kylebernier/lambda-oxygen-sensor-interface/verification/DAC_air_comp.csv

#Digilent WaveForms Oscilloscope Acquisition
#Device Name: Discovery2
#Serial Number: SN:210321A36376
#Date Time: 2019-03-14 15:58:00.707
#Sample rate: 800000Hz
#Samples: 8192
#Trigger: Source: Channel 1 Type: Edge Condition: Rising Level: 2.95 V Hyst.: Auto HoldOff: 0 s
#Channel 1: Range: 500 mV/div Offset: -500 mV
#Channel 2: Range: 500 mV/div Offset: -500 mV
#Math 2: Function: (C1-C2)/0.00017053
Time (s) | Channel 1 (V) | Channel 2 (V) | Math 2 (Ω)
-0.00512 | -0.0240829 | -0.00160749 | -131.798
-0.00511875 | -0.0244141 | -0.00127197 | -135.707
-0.0051175 | -0.0237517 | -0.00160749 | -129.855
-0.00511625 | -0.0240829 | -0.00127197 | -133.765
-0.005115 | -0.0237517 | -0.00160749 | -129.855
-0.00511375 | -0.0244141 | -0.00127197 | -135.707
-0.0051125 | -0.0237517 | -0.000936452 | -133.79
-0.00511125 | -0.0234205 | -0.000936452 | -131.848
-0.00511 | -0.0240829 | -0.000936452 | -135.733
-0.00510875 | -0.0234205 | -0.000936452 | -131.848
-0.0051075 | -0.0247453 | -0.00160749 | -135.682
-0.00510625 | -0.0247453 | -0.001943 | -133.714
-0.005105 | -0.0247453 | -0.00127197 | -137.649
-0.00510375 | -0.0250765 | -0.000936452 | -141.559
-0.0051025 | -0.0247453 | -0.000936452 | -139.617
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
