kylebernier/lambda-oxygen-sensor-interface/verification/PureLambda.csv

#Digilent WaveForms Oscilloscope Acquisition
#Device Name: Discovery2
#Serial Number: SN:210321A36376
#Date Time: 2019-04-09 16:56:31.763
#Sample rate: 400000Hz
#Samples: 8192
#Trigger: Source: Channel 1 Type: Edge Condition: Either Level: 3 V Hyst.: Auto HoldOff: 0 s
#Our λ: Function: C1/5*(1.36-0.65)+0.65
Time (s) | Our λ (λ)
-0.0102375 | 1.20195
-0.010235 | 1.20144
-0.0102325 | 1.20144
-0.01023 | 1.20144
-0.0102275 | 1.20195
-0.010225 | 1.20298
-0.0102225 | 1.20247
-0.01022 | 1.2035
-0.0102175 | 1.20298
-0.010215 | 1.20298
-0.0102125 | 1.20247
-0.01021 | 1.20298
-0.0102075 | 1.2035
-0.010205 | 1.2035
-0.0102025 | 1.2035
-0.0102 | 1.20402
-0.0101975 | 1.2035
-0.010195 | 1.2035
-0.0101925 | 1.2035
-0.01019 | 1.20505
-0.0101875 | 1.20453
-0.010185 | 1.20453
-0.0101825 | 1.20505
-0.01018 | 1.20505
-0.0101775 | 1.20505
-0.010175 | 1.20505
-0.0101725 | 1.20557
-0.01017 | 1.20557
-0.0101675 | 1.20557
-0.010165 | 1.20608
-0.0101625 | 1.20557
-0.01016 | 1.20557
-0.0101575 | 1.20557
-0.010155 | 1.20712
-0.0101525 | 1.2066
-0.01015 | 1.20608
-0.0101475 | 1.20712
-0.010145 | 1.20608
-0.0101425 | 1.2066
-0.01014 | 1.2066
-0.0101375 | 1.20712
-0.010135 | 1.20763
-0.0101325 | 1.20763
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
