kylebernier/lambda-oxygen-sensor-interface/sim/heater.asc

R1: res; 0.84
R3: res; 7.5
U2: ntd5865nl
V1: voltage; 12
V3: voltage; PULSE(0 5 5m 8n 7n 5m 10m)
Named nets: 0, OUT, IN
.tran 0 0.1 0 0.1u
