kylebernier/lambda-oxygen-sensor-interface/sim/power.asc

C1: cap; 22µ; V=200
C2: cap; 2.2µ
C3: cap; 22µ; V=200
R1: res; 510k
R2: res; 6.34Meg
R3: res; 95.3k
R4: res; 205k
R5: res; 100k
U1: LTC4367
U2: SQJ974EP
U3: SQJ974EP
U13: SMAJ58CA
V1: voltage; PWL(0 0 +20u 12 +.1 12 +20u 80; +.3 12 +.1 12 +20u 200 +1m 200
Named nets: 0, 12V, VBAT, fault, out
.tran .7
